sciguy14/blumbike/blumbike_web_app/assets/android-chrome-192x192.png

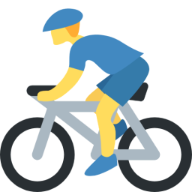
blumbike_web_app/assets/android-chrome-192x192.png
